Five-Dynamics/AvionicsPCBs/Polaris/Rocket.kicad_sch

## KiCad design Polaris/Rocket.kicad_sch (2025-04-04)

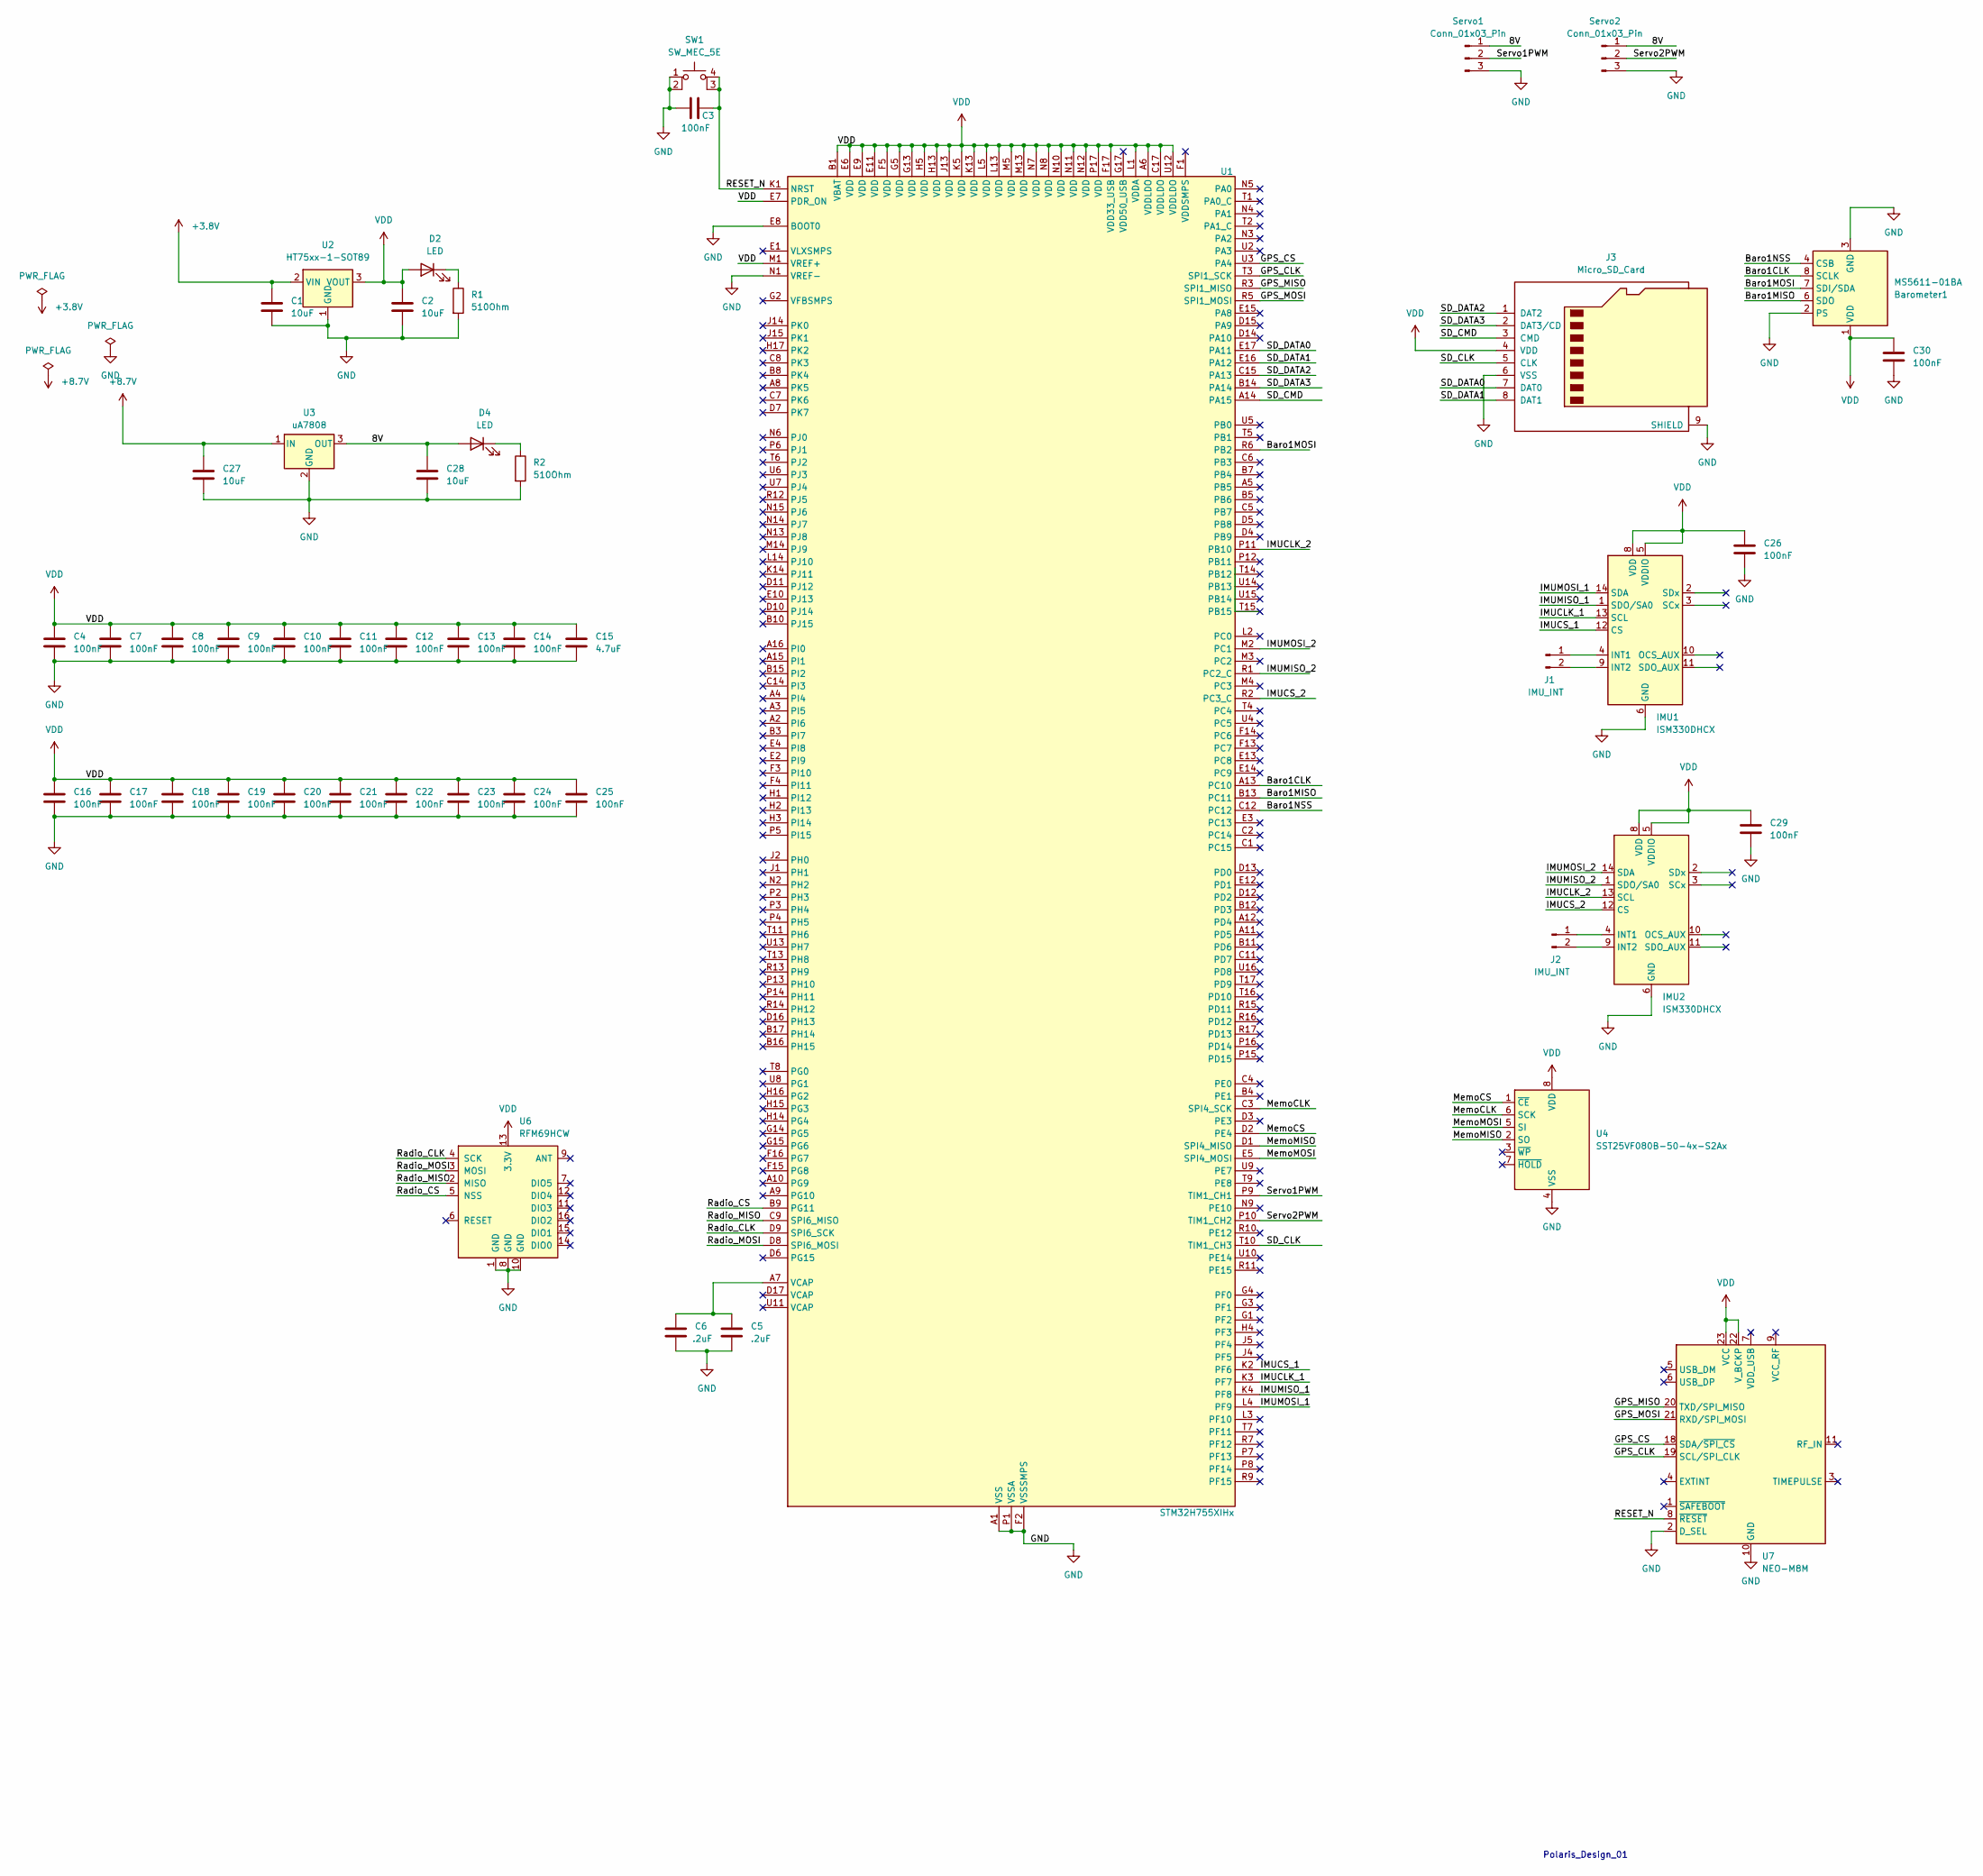
[picture p3: schematic Rocket.kicad_sch]

Parts:
Barometer1: MS5611-01BA; LGA-8_3x5mm_P1.25mm
C1, C27: 10uF; C_0201_0603Metric_Pad0.64x0.40mm_HandSolder
C2, C28: 10uF; C_0402_1005Metric
C3, C4, C7, C8, C9, C10, C11, C12, C13, C14, C16, C17, C18, C19, C20, C21, C22, C23, C24, C25, C26, C29, C30: 100nF; C_0402_1005Metric
C5, C6: .2uF; C_0402_1005Metric
C15: 4.7uF; C_0402_1005Metric
D2, D4: LED; LED_D3.0mm_Horizontal_O6.35mm_Z10.0mm
IMU1, IMU2: ISM330DHCX; LGA-14_3x2.5mm_P0.5mm_LayoutBorder3x4y
J1, J2: IMU_INT; SolderWire-1sqmm_1x02_P5.4mm_D1.4mm_OD2.7mm
J3: Micro_SD_Card
R1, R2: 510Ohm; R_0201_0603Metric
SW1: SW_MEC_5E; SW_MEC_5GSH9
Servo1, Servo2: Conn_01x03_Pin; FanPinHeader_1x03_P2.54mm_Vertical
U1: STM32H755XIHx; TFBGA-265_14x14mm_Layout17x17_P0.8mm
U2: HT75xx-1-SOT89; SOT-89-3
U3: uA7808; TO-220-3_Vertical
U4: SST25VF080B-50-4x-S2Ax; SOIC-8_5.275x5.275mm_P1.27mm
U6: RFM69HCW; HOPERF_RFM9XW_SMD
U7: NEO-M8M; ublox_NEO

Connections:
8V: C28.1, D4.2 (A), Servo1.1, Servo2.1, U3.3 (OUT)
+3.8V: C1.1, U2.2 (VIN)
+8.7V: C27.1, U3.1 (IN)
Baro1CLK: Barometer1.8 (SCLK), U1.A13 (PC10)
Baro1MISO: Barometer1.6 (SDO), U1.B13 (PC11)
Baro1MOSI: Barometer1.7 (SDI/SDA), U1.R6 (PB2)
Baro1NSS: Barometer1.4 (CSB), Barometer1.5 (CSB), U1.C12
GND: Barometer1.2 (PS), Barometer1.3 (GND), C1.2, C2.2, C3.2, C4.2, C5.2, C6.2, C7.2, C8.2, C9.2, C10.2, C11.2, C12.2, C13.2, C14.2, C15.2, C16.2, C17.2, C18.2, C19.2, C20.2, C21.2, C22.2, C23.2, C24.2, C25.2, C26.2, C27.2, C28.2, C29.2, C30.2, IMU1.6 (GND), IMU1.7 (GND), IMU2.6 (GND), IMU2.7 (GND), J3.6 (VSS), J3.9 (SHIELD), R1.2, R2.2, SW1.1, SW1.2, Servo1.3, Servo2.3, U1.A1 (VSS), U1.A17 (VSS), U1.B2 (VSS), U1.B6 (VSS), U1.C10 (VSS), U1.C13 (VSS), U1.C16 (VSS), U1.E8 (BOOT0), U1.F2 (VSSSMPS), U1.G7 (VSS), U1.G8 (VSS), U1.G9 (VSS), U1.G10 (VSS), U1.G11 (VSS), U1.G16 (VSS), U1.H7 (VSS), U1.H8 (VSS), U1.H9 (VSS), U1.H10 (VSS), U1.H11 (VSS), U1.J3 (VSS), U1.J7 (VSS), U1.J8 (VSS), U1.J9 (VSS), U1.J10 (VSS), U1.J11 (VSS), U1.J16 (VSS), U1.J17 (VSS), U1.K7 (VSS), U1.K8 (VSS), U1.K9 (VSS), U1.K10 (VSS), U1.K11 (VSS), U1.K15 (VSS), U1.L7 (VSS), U1.L8 (VSS), U1.L9 (VSS), U1.L10 (VSS), U1.L11 (VSS), U1.L15 (VSS), U1.M15 (VSS), U1.N1 (VREF-), U1.N16 (VSS), U1.P1 (VSSA), U1.R4 (VSS), U1.R8 (VSS), U1.T12 (VSS), U1.U1 (VSS), U1.U17 (VSS), U2.1 (GND), U3.2 (GND), U4.4 (VSS), U6.1 (GND), U6.8 (GND), U6.10 (GND), U7.2 (D_SEL), U7.10 (GND), U7.12 (GND), U7.13 (GND), U7.24 (GND)
GPS_CLK: U1.T3 (PA5), U7.19 (SCL/SPI_CLK)
GPS_CS: U1.U3 (PA4), U7.18 (SDA/~SPI_CS)
GPS_MISO: U1.R3 (PA6), U7.20 (TXD/SPI_MISO)
GPS_MOSI: U1.R5 (PA7), U7.21 (RXD/SPI_MOSI)
IMUCLK_1: IMU1.13 (SCL), U1.K3 (PF7)
IMUCLK_2: IMU2.13 (SCL), U1.P11 (PB10)
IMUCS_1: IMU1.12 (CS), U1.K2 (PF6)
IMUCS_2: IMU2.12 (CS), U1.R2 (PC3_C)
IMUMISO_1: IMU1.1 (SDO/SA0), U1.K4 (PF8)
IMUMISO_2: IMU2.1 (SDO/SA0), U1.R1 (PC2_C)
IMUMOSI_1: IMU1.14 (SDA), U1.L4 (PF9)
IMUMOSI_2: IMU2.14 (SDA), U1.M2 (PC1)
MemoCLK: U1.C3 (PE2), U4.6 (SCK)
MemoCS: U1.D2 (PE4), U4.1 (~CE)
MemoMISO: U1.D1 (PE5), U4.2 (SO)
MemoMOSI: U1.E5 (PE6), U4.5 (SI)
unnamed: C5.1, C6.1, U1.A7 (VCAP)
unnamed: D2.1 (K), R1.1
unnamed: D4.1 (K), R2.1
unnamed: IMU1.4 (INT1), J1.1
unnamed: IMU1.9 (INT2), J1.2
unnamed: IMU2.4 (INT1), J2.1
unnamed: IMU2.9 (INT2), J2.2
RESET_N: C3.1, SW1.3 (K), SW1.4 (A), U1.K1 (NRST), U7.8 (~RESET)
Radio_CLK: U1.D9 (PG13), U6.4 (SCK)
Radio_CS: U1.B9 (PG11), U6.5 (NSS)
Radio_MISO: U1.C9 (PG12), U6.2 (MISO)
Radio_MOSI: U1.D8 (PG14), U6.3 (MOSI)
SD_CLK: J3.5 (CLK), U1.T10 (PE13)
SD_CMD: J3.3 (CMD), U1.A14 (PA15)
SD_DATA0: J3.7 (DAT0), U1.E17 (PA11)
SD_DATA1: J3.8 (DAT1), U1.E16 (PA12)
SD_DATA2: J3.1 (DAT2), U1.C15 (PA13)
SD_DATA3: J3.2 (DAT3/CD), U1.B14 (PA14)
Servo1PWM: Servo1.2, U1.P9 (PE9)
Servo2PWM: Servo2.2, U1.P10 (PE11)
VDD: Barometer1.1 (VDD), C2.1, C4.1, C7.1, C8.1, C9.1, C10.1, C11.1, C12.1, C13.1, C14.1, C15.1, C16.1, C17.1, C18.1, C19.1, C20.1, C21.1, C22.1, C23.1, C24.1, C25.1, C26.1, C29.1, C30.1, D2.2 (A), IMU1.5 (VDDIO), IMU1.8 (VDD), IMU2.5 (VDDIO), IMU2.8 (VDD), J3.4 (VDD), U1.A6 (VDDLDO), U1.B1 (VBAT), U1.C17 (VDDLDO), U1.E6 (VDD), U1.E7 (PDR_ON), U1.E9 (VDD), U1.E11 (VDD), U1.F5 (VDD), U1.F17 (VDD33_USB), U1.G5 (VDD), U1.G13 (VDD), U1.H5 (VDD), U1.H13 (VDD), U1.J13 (VDD), U1.K5 (VDD), U1.K13 (VDD), U1.L1 (VDDA), U1.L5 (VDD), U1.L13 (VDD), U1.M1 (VREF+), U1.M5 (VDD), U1.M13 (VDD), U1.N7 (VDD), U1.N8 (VDD), U1.N10 (VDD), U1.N11 (VDD), U1.N12 (VDD), U1.P17 (VDD), U1.U12 (VDDLDO), U2.3 (VOUT), U4.8 (VDD), U6.13 (3.3V), U7.22 (V_BCKP), U7.23 (VCC)

Notes on the sheet:
Polaris_Design_01
